asinghani/mpw3-bringup/programs/gpio_config_io_dino.py

# number of IO in the configuration stream for each chain
NUM_IO = 19

# defines these values for IO configurations
C_MGMT_OUT = 0
C_MGMT_IN = 1
C_USER_BIDIR = 2
C_DISABLE = 3
C_ALL_ONES = 4
C_USER_BIDIR_WPU = 5
C_USER_BIDIR_WPD = 6
C_USER_IN_NOPULL = 7
C_USER_OUT = 8

"""
`define DINO2_JUMP_PIN 27
`define DINO2_HALT_PIN 28
`define DINO2_DBG_PIN  29
`define DINO2_VS_PIN   30
`define DINO2_HS_PIN   31

`define DINO2_PIX_PIN  32
"""


config_h = [
    C_MGMT_OUT,  #37
    C_MGMT_OUT,  #36
    C_MGMT_OUT,  #35
    C_MGMT_OUT,  #34
    C_MGMT_OUT,  #33
    C_USER_OUT,  #32
    C_USER_OUT,  #31
    C_USER_OUT,  #30
    C_USER_IN_NOPULL,  #29
    C_USER_IN_NOPULL,  #28
    C_USER_IN_NOPULL,  #27
    C_MGMT_OUT,  #26
    C_MGMT_OUT,  #25
    C_MGMT_OUT,  #24
    C_MGMT_OUT,  #23
    C_MGMT_OUT,  #22
    C_MGMT_OUT,  #21
    C_MGMT_OUT,  #20
    C_MGMT_OUT,  #19
]

del config_h[NUM_IO:]

config_l = [
    C_MGMT_OUT,   #0
    C_MGMT_OUT,   #1
    C_MGMT_OUT,   #2
    C_MGMT_OUT,   #3
    C_MGMT_OUT,   #4
    C_MGMT_OUT,   #5
    C_MGMT_OUT,   #6
    C_MGMT_OUT,   #7
    C_MGMT_OUT,   #8
    C_MGMT_OUT,   #9
    C_MGMT_OUT,   #10
    C_MGMT_OUT,   #11
    C_MGMT_OUT,   #12
    C_MGMT_OUT,   #13
    C_MGMT_OUT,   #14
    C_MGMT_OUT,   #15
    C_MGMT_OUT,   #16
    C_MGMT_OUT,   #17
    C_MGMT_OUT,   #18
]

del config_l[NUM_IO:]
